09labs/Hangul-Clock/HangulClock-Arduino/Hangul.cpp

#include "Arduino.h"
#include "Hangul.h"

Hangul::Hangul(uint8_t pin, uint8_t numpixels){
  _pin = pin;
  _numpixels = numpixels;
}
void Hangul::AMPM(uint8_t hours){
  if(hours == 0 || hours == 24)
  {
    pixels.setPixelColor(0,color);
    pixels.setPixelColor(1,color);
    pixels.setPixelColor(2,pixels.Color(0,0,0));
  }
  else if(hours >= 12 && hours <=23)
  {
    pixels.setPixelColor(0,color);
    pixels.setPixelColor(1,pixels.Color(0,0,0));
    pixels.setPixelColor(2,color);
  }
  else if(hours < 12 && hours >= 1)
  {
    pixels.setPixelColor(0,color);
    pixels.setPixelColor(1,color);
    pixels.setPixelColor(2,pixels.Color(0,0,0));
  }
  else;
}
void Hangul::hourChange(uint8_t hours, uint8_t minutes){
  uint8_t ConvertHour = 0;

  if(hours >= 12){
    ConvertHour = hours - 12;
  }
  else{
    ConvertHour = hours;
  }
  switch(ConvertHour)
  {
    case 0:
    {
      pixels.setPixelColor(6, color);
      pixels.setPixelColor(7, pixels.Color(0,0,0));
      pixels.setPixelColor(8, color);
      for(int i = 9 ; i < 20 ; i++)
      {
        pixels.setPixelColor(i, pixels.Color(0,0,0));
      }
      break;
    }
    case 1:
    {
      pixels.setPixelColor(6, pixels.Color(0,0,0));
      pixels.setPixelColor(7, color);
      for(int i = 8 ; i < 20 ; i++)
      {
        pixels.setPixelColor(i, pixels.Color(0,0,0));
      }
      break;
    }
    case 2:
    {
      pixels.setPixelColor(6, pixels.Color(0,0,0));
      pixels.setPixelColor(7, pixels.Color(0,0,0));
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
      pixels.setPixelColor(31, pixels.Color(0,0,0));
      pixels.setPixelColor(32, pixels.Color(0,0,0));
      pixels.setPixelColor(33, pixels.Color(0,0,0));
      pixels.setPixelColor(34, pixels.Color(0,0,0));
    }
    else if(one == 6){
      for(int i = 26 ; i < 29 ; i ++)
      {
        pixels.setPixelColor(i, pixels.Color(0,0,0));
      }
      pixels.setPixelColor(29, color);
      for(int i = 30 ; i < 35 ; i ++)
      {
        pixels.setPixelColor(i, pixels.Color(0,0,0));
      }
    }
    else if(one == 7){
      for(int i = 26 ; i < 28 ; i ++)
      {
        pixels.setPixelColor(i, pixels.Color(0,0,0));
      }
      pixels.setPixelColor(28, color);
      for(int i = 29 ; i < 35 ; i ++)
      {
        pixels.setPixelColor(i, pixels.Color(0,0,0));
      }
    }
    else if(one == 8){
      pixels.setPixelColor(26, pixels.Color(0,0,0));
      pixels.setPixelColor(27, color);
      for(int i = 28 ; i < 35 ; i ++)
      {
        pixels.setPixelColor(i, pixels.Color(0,0,0));
      }
    }
    else if(one == 9){
      pixels.setPixelColor(26, color);
      for(int i = 27 ; i < 35 ; i ++)
      {
        pixels.setPixelColor(i, pixels.Color(0,0,0));
      }
    }
    pixels.setPixelColor(35, color);
  }
  
}
void Hangul::resetLED(){
  for(uint8_t i = 0 ; i < 36 ; i++)
  {
    pixels.setPixelColor(i, pixels.Color(0,0,0));
    pixels.show();
  }
  
}

void Hangul::setTimee(String input){
  uint8_t Hours, Minutes, Seconds=0;
  uint8_t first_c, seconds_c;

  first_c = input.indexOf(":");
  seconds_c = input.indexOf(":", first_c+1);

  Hours = input.substring(0,first_c).toInt();
  Minutes = input.substring(first_c+1, seconds_c).toInt();
  Seconds = input.substring(seconds_c+1).toInt();  

  _time.hours = Hours;
  _time.minutes = Minutes;
  _time.secs = Seconds;
}
void Hangul::blinkSec(){
  uint8_t b = 0;

  b = _time.secs % 2;
  if(b == 1){
    pixels.setPixelColor(3,color);
    pixels.setPixelColor(4,color);
    pixels.setPixelColor(5,color);
  }
  else{
    pixels.setPixelColor(3,0);
    pixels.setPixelColor(4,0);
    pixels.setPixelColor(5,0);
  }
  
}
void Hangul::updateTime(){

  blinkSec();
  AMPM(_time.hours);
  hourChange(_time.hours,_time.minutes);
  minuteChange(_time.minutes);
  pixels.show();
  if((_time.secs != _old_secs) && _time.secs == 0){
    resetLED();
  }
  _old_secs = _time.secs;
  /*
  _time.secs += 1;
  
  if(_time.secs == 60){
    resetLED();
    _time.secs = 0;
    _time.minutes += 1;
  }
  if(_time.minutes == 60){
    _time.minutes = 0; 
    _time.hours += 1;
  }
  if(_time.hours == 24){
    _time.hours = 0;
  }*/
}

void Hangul::colorChange(){
  uint8_t red, green, blue;
  red = digitalRead(6);
  green = digitalRead(7);
  blue = digitalRead(8);
  
    if((old_r != red) && (red == 1)){
      _red += 10;
      if(_red > 250){
        _red = 0;
      }
      color = pixels.Color(_red, _green, _blue);
      pixels.show();
    }
    

    if((old_g != green) && (green == 1)){
      _green += 10;
      if(_green > 250)
      {
        _green = 0;
      }
      color = pixels.Color(_red, _green, _blue);
      pixels.show();
    }
  
    if((old_b != blue) && (blue == 1)){
      
      _blue += 10;
      if(_blue > 250){
        _blue = 0;
      }
      color = pixels.Color(_red, _green, _blue);
      pixels.show();
    }
  
  old_r = red;
  old_g = green;
  old_b = blue;
}
